dulouie/mushroom_mppt/docs/dist/pictures/beide.jpg

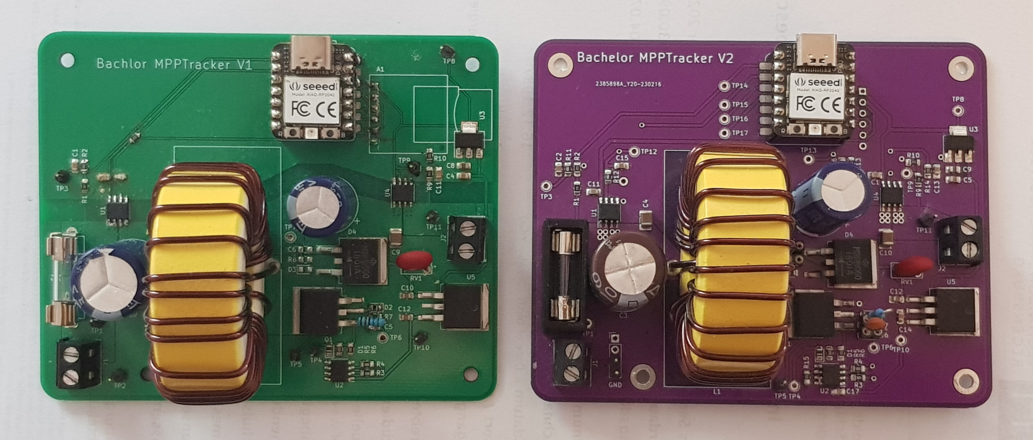
docs/dist/pictures/beide.jpg
