dulouie/mushroom_mppt/docs/dist/pictures/iu-kennlinie.png

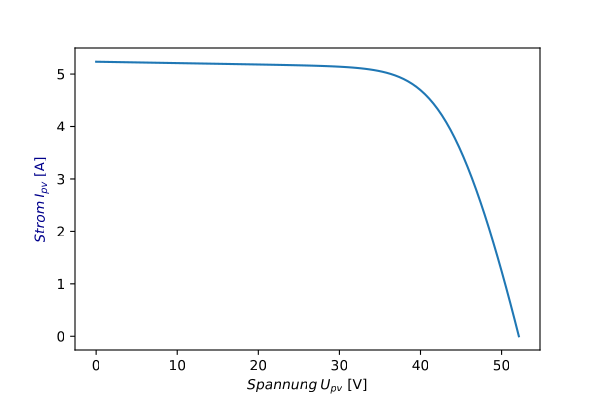
docs/dist/pictures/iu-kennlinie.png
