dulouie/mushroom_mppt/docs/dist/pictures/konzept1.png

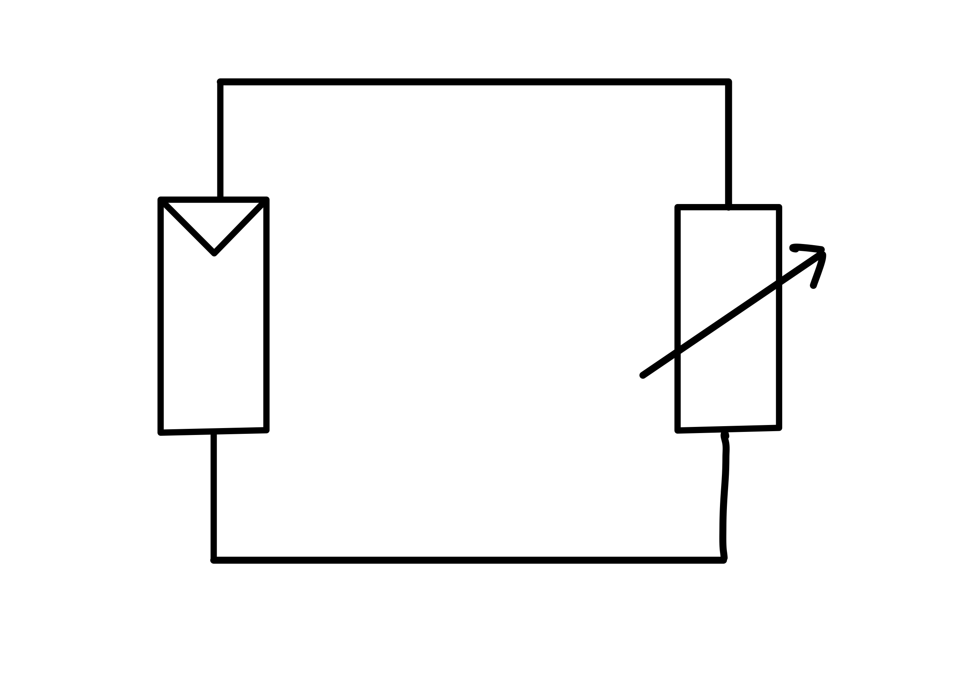
docs/dist/pictures/konzept1.png
