dulouie/mushroom_mppt/docs/dist/pictures/konzept2.png

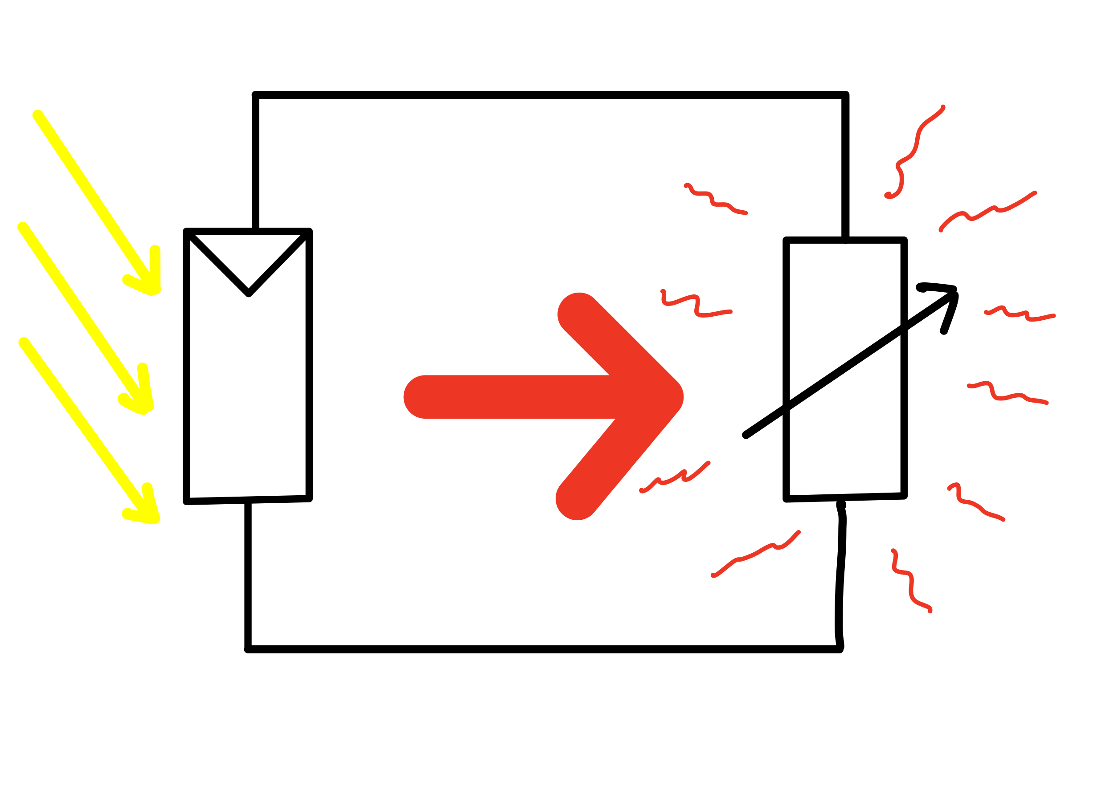
docs/dist/pictures/konzept2.png
