dulouie/mushroom_mppt/docs/dist/pictures/konzept6.png

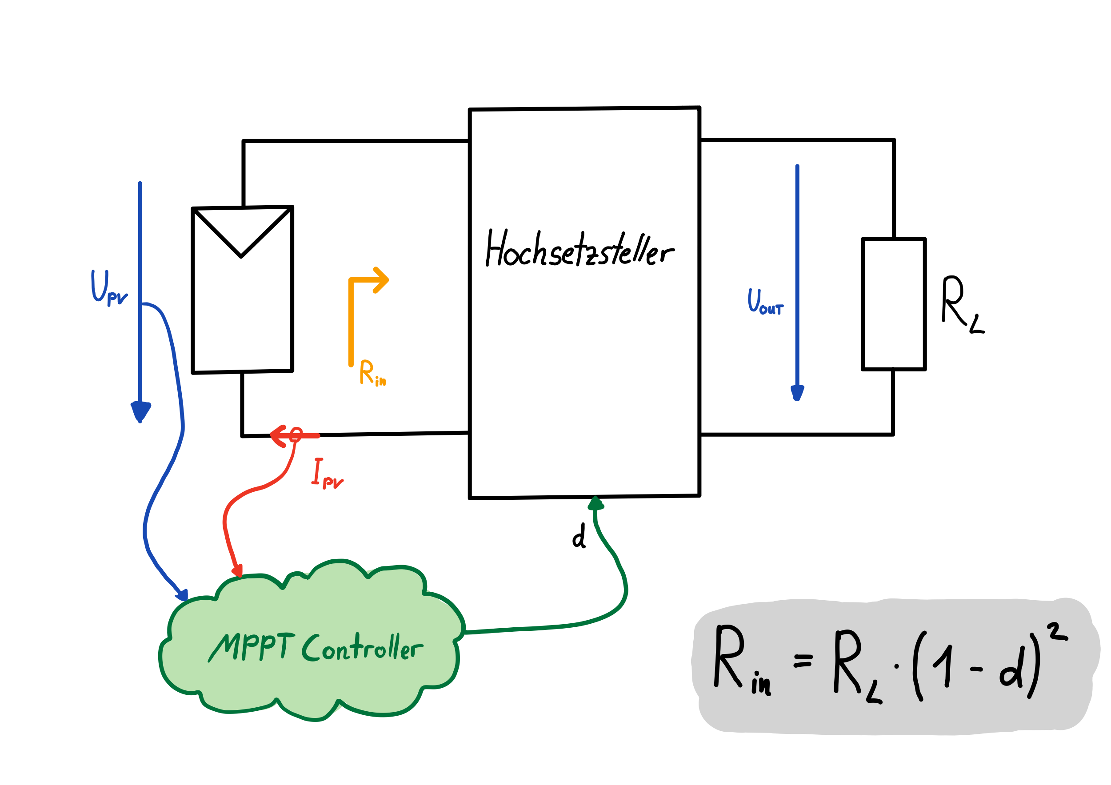
docs/dist/pictures/konzept6.png
