dulouie/mushroom_mppt/docs/dist/pictures/konzept7.png

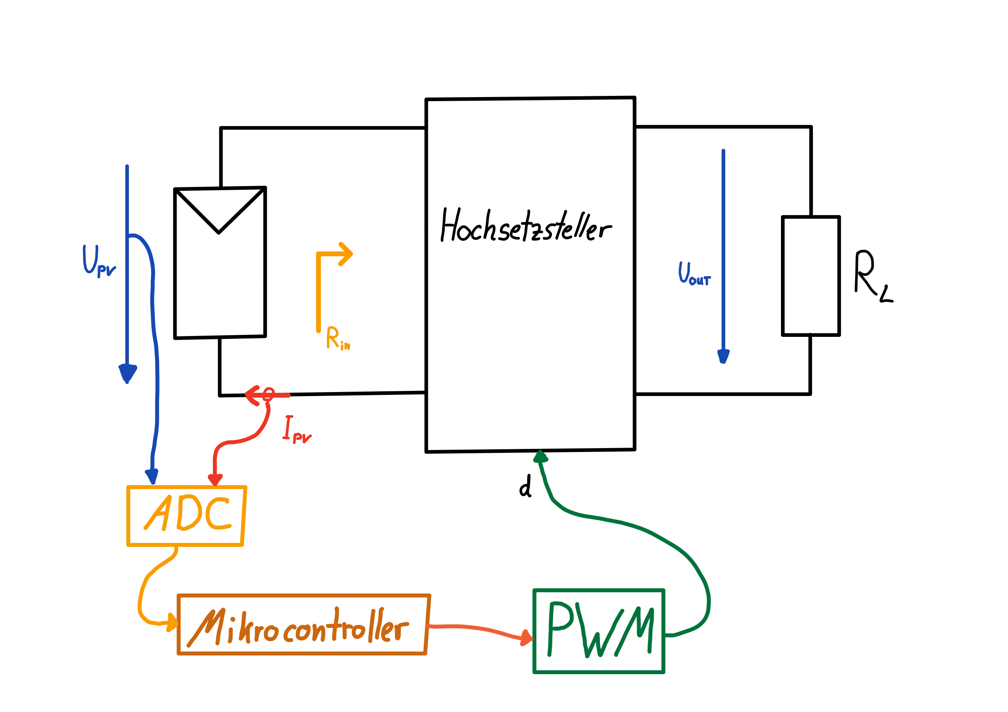
docs/dist/pictures/konzept7.png
