dulouie/mushroom_mppt/docs/dist/pictures/layout1.png

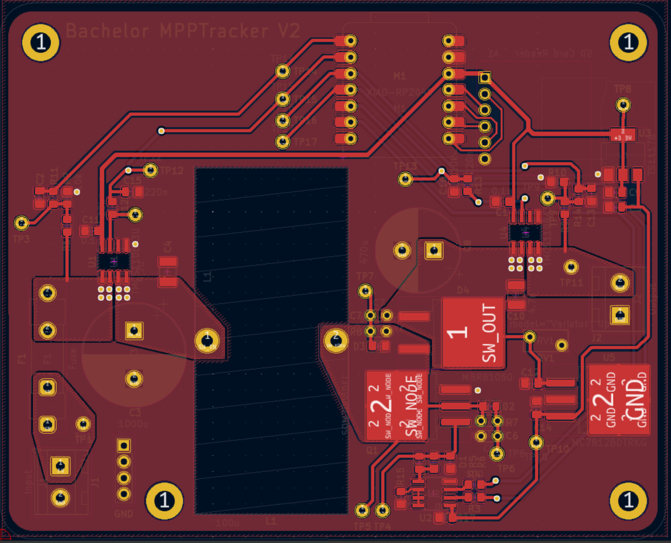
docs/dist/pictures/layout1.png
