dulouie/mushroom_mppt/docs/dist/pictures/leistungswiderstand.jpg

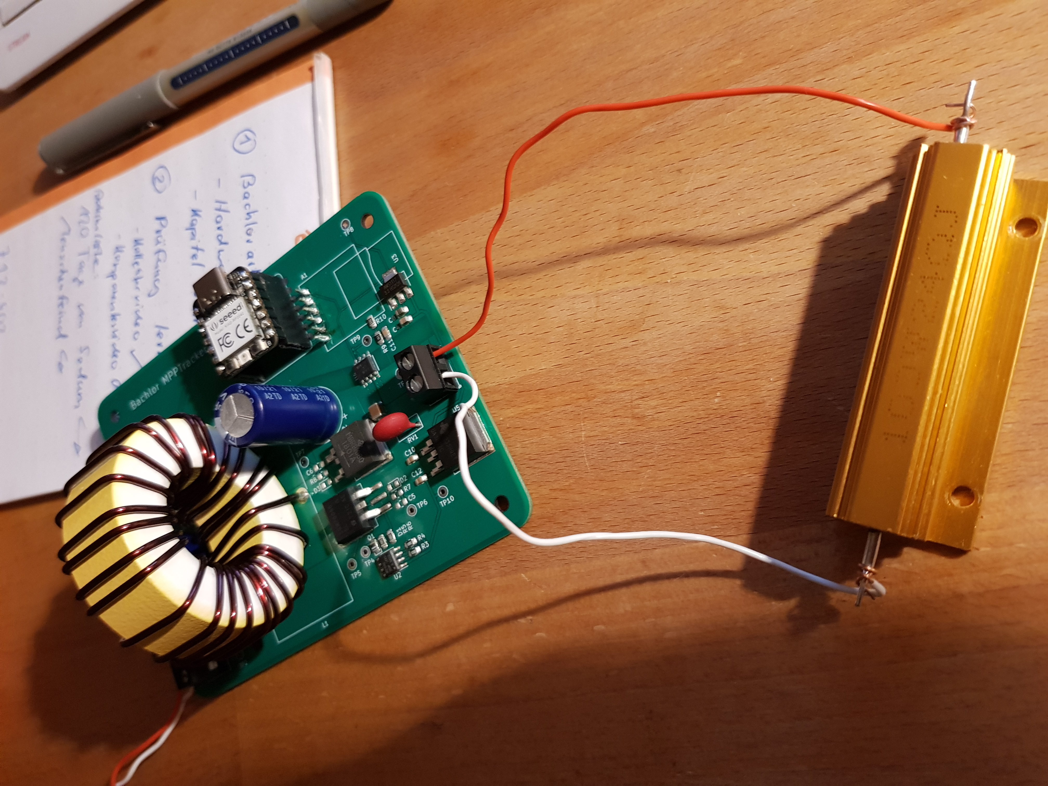
docs/dist/pictures/leistungswiderstand.jpg
