dulouie/mushroom_mppt/docs/dist/pictures/messen.jpg

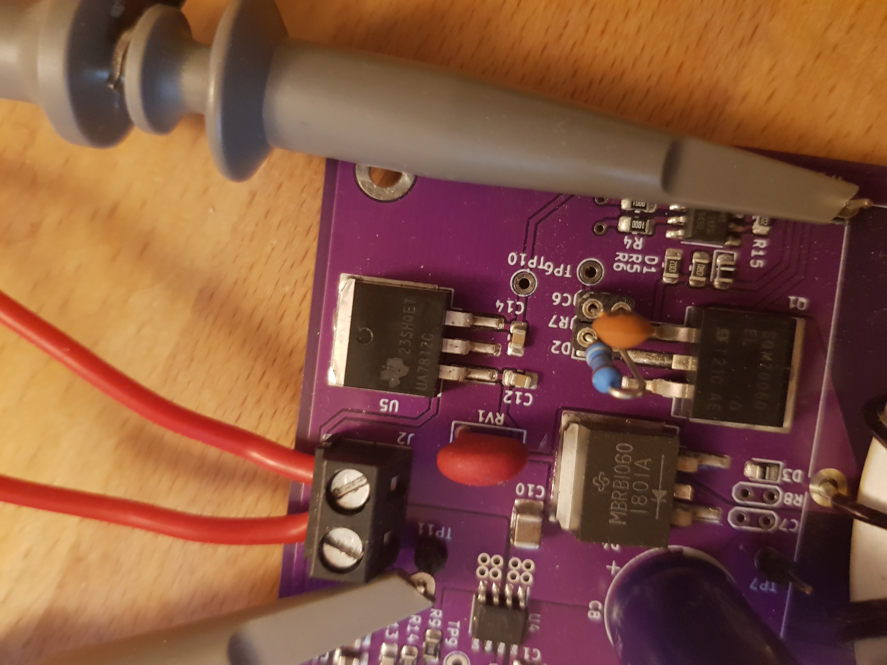
docs/dist/pictures/messen.jpg
