dulouie/mushroom_mppt/docs/dist/pictures/mosfet.jpg

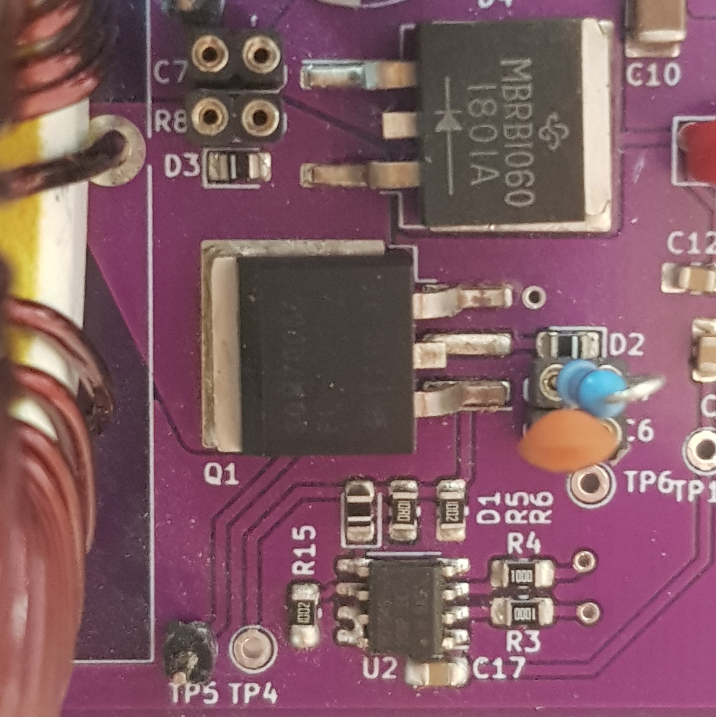
docs/dist/pictures/mosfet.jpg
