dulouie/mushroom_mppt/docs/dist/pictures/pico.jpg

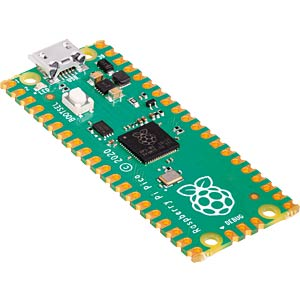
docs/dist/pictures/pico.jpg
