dulouie/mushroom_mppt/docs/dist/pictures/pvemulator.jpg

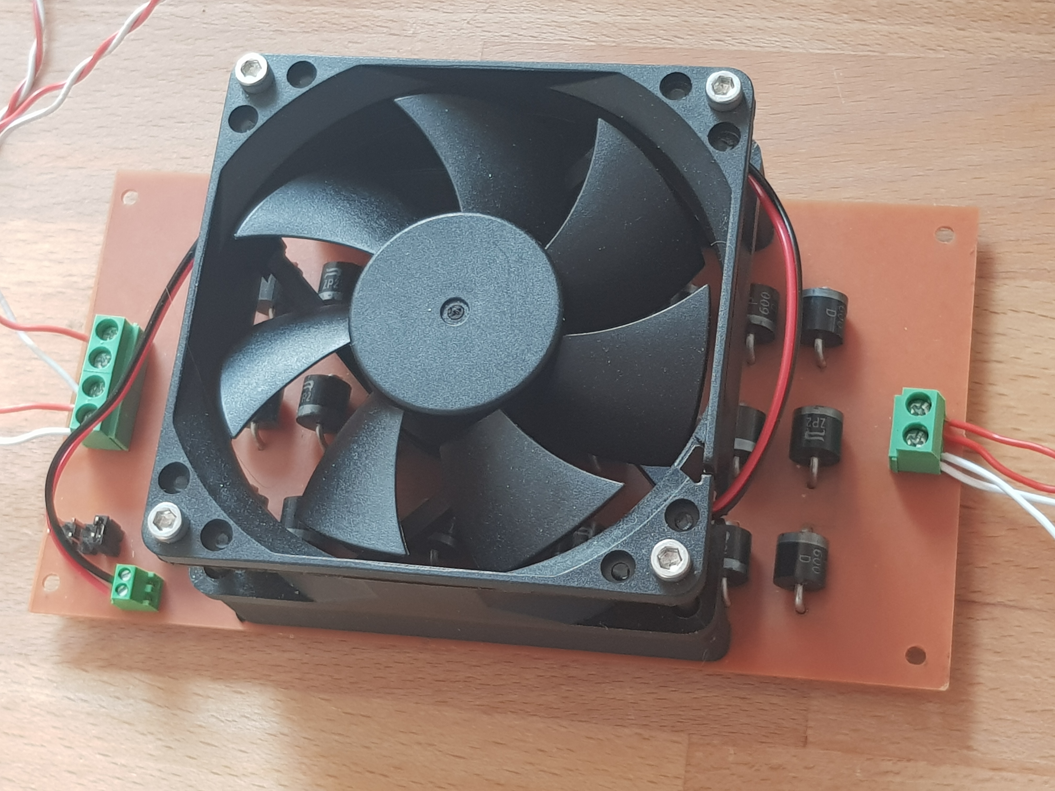
docs/dist/pictures/pvemulator.jpg
