dulouie/mushroom_mppt/docs/dist/pictures/rp2040.jpg

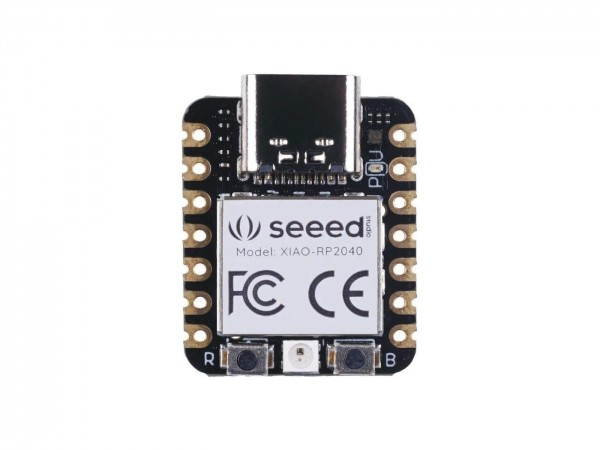
docs/dist/pictures/rp2040.jpg
