dulouie/mushroom_mppt/docs/dist/pictures/schaltplan_alt.png

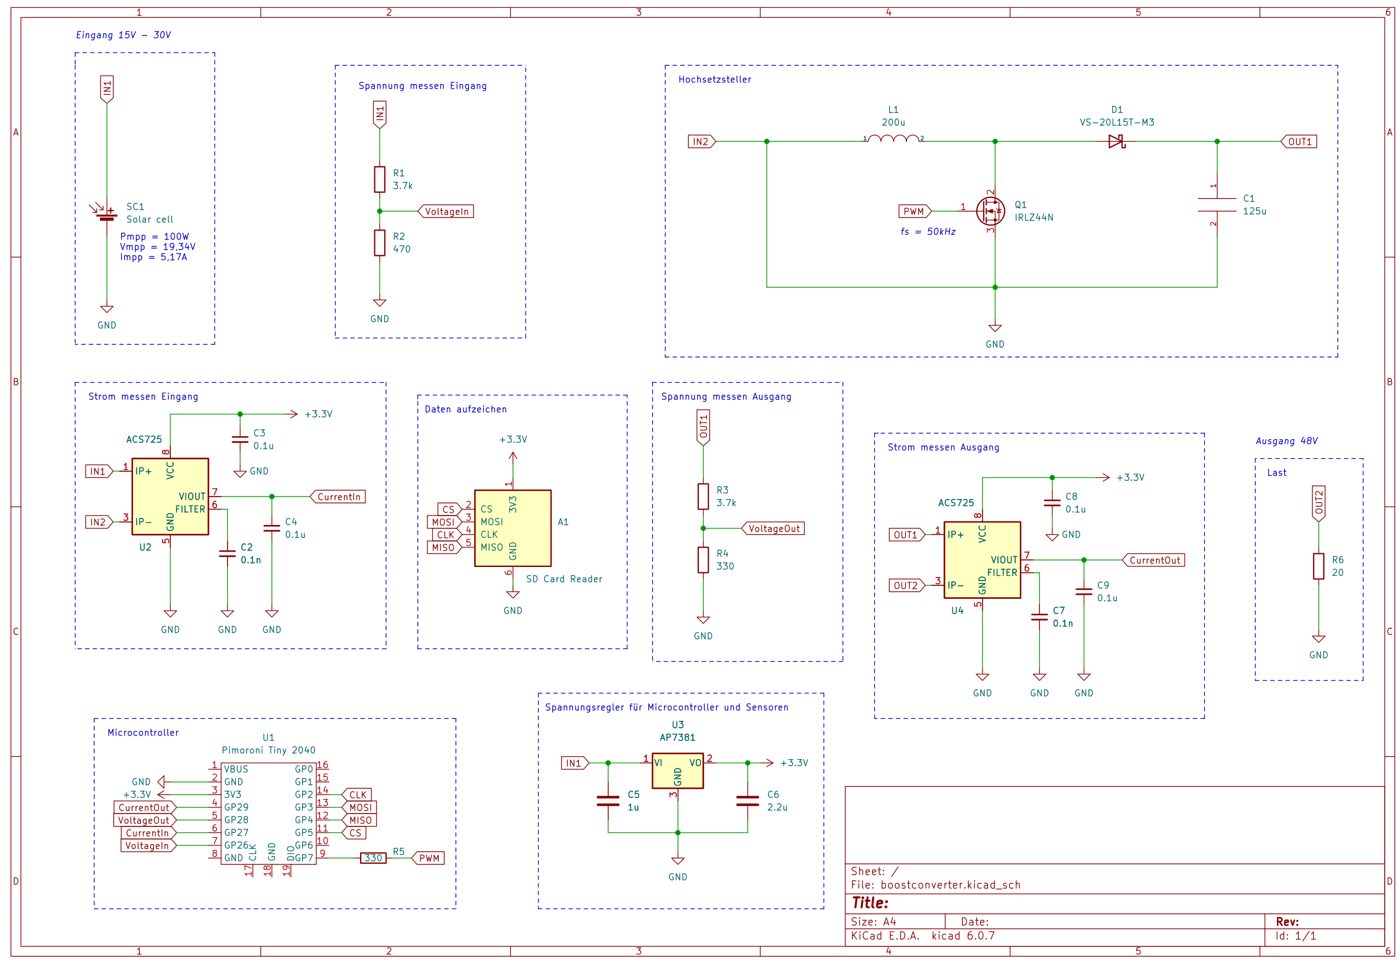
docs/dist/pictures/schaltplan_alt.png
