dulouie/mushroom_mppt/docs/dist/pictures/smd2.jpg

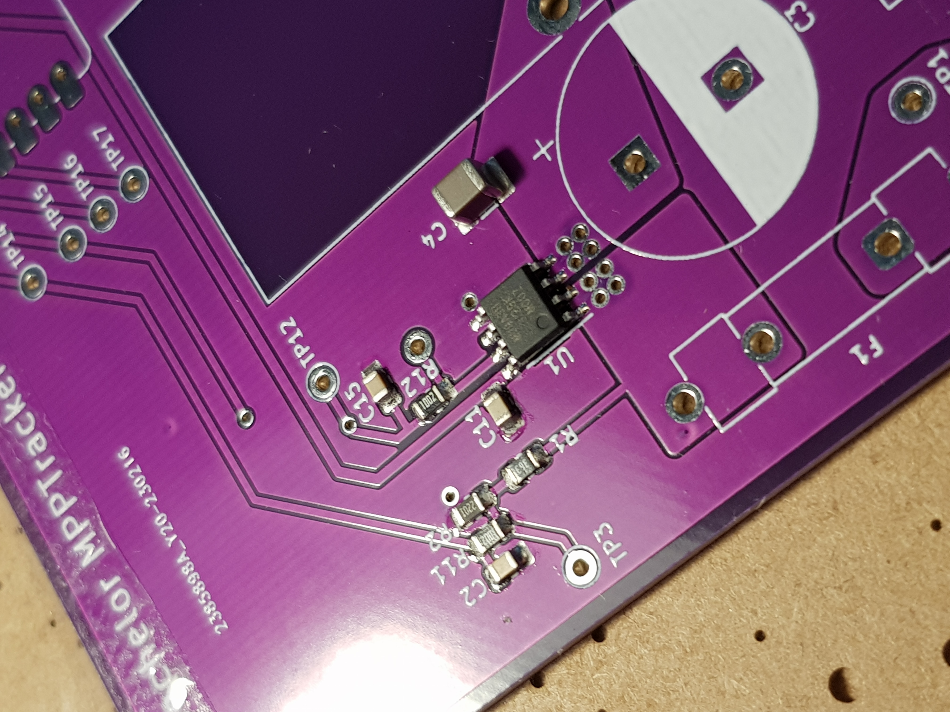
docs/dist/pictures/smd2.jpg
