dulouie/mushroom_mppt/docs/dist/pictures/smd3.jpg

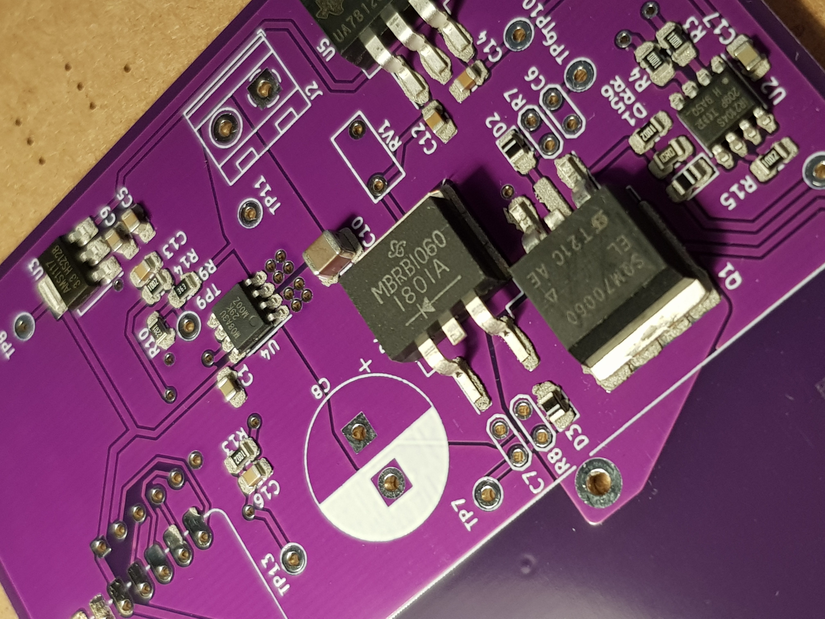
docs/dist/pictures/smd3.jpg
