dulouie/mushroom_mppt/docs/dist/pictures/smd4.jpg

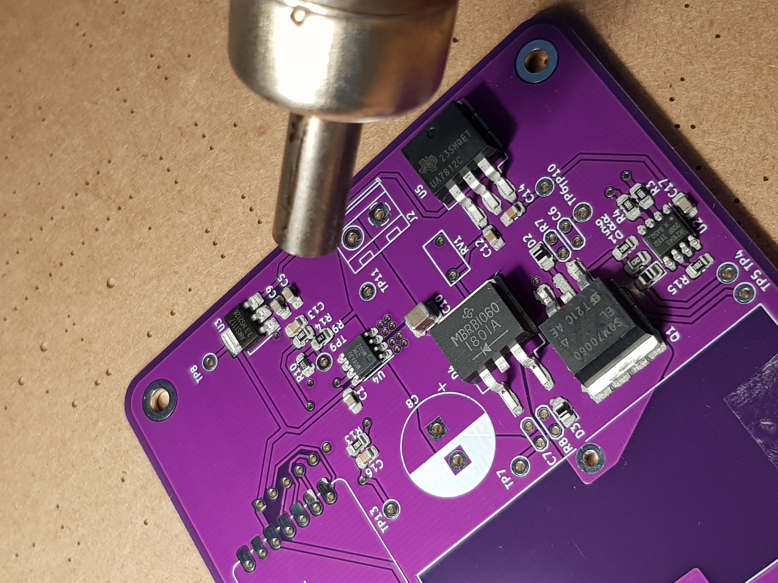
docs/dist/pictures/smd4.jpg
