dulouie/mushroom_mppt/docs/dist/pictures/snubber-ring.png

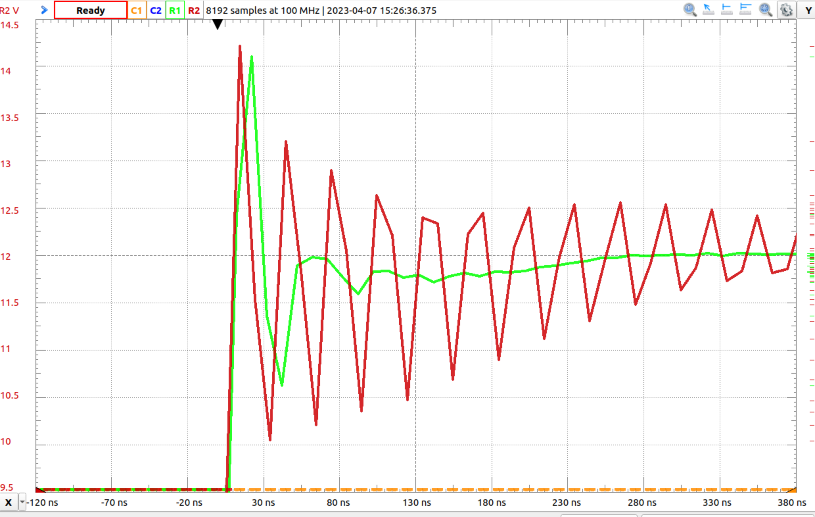
docs/dist/pictures/snubber-ring.png
