dulouie/mushroom_mppt/docs/dist/pictures/spannungsteiler.jpg

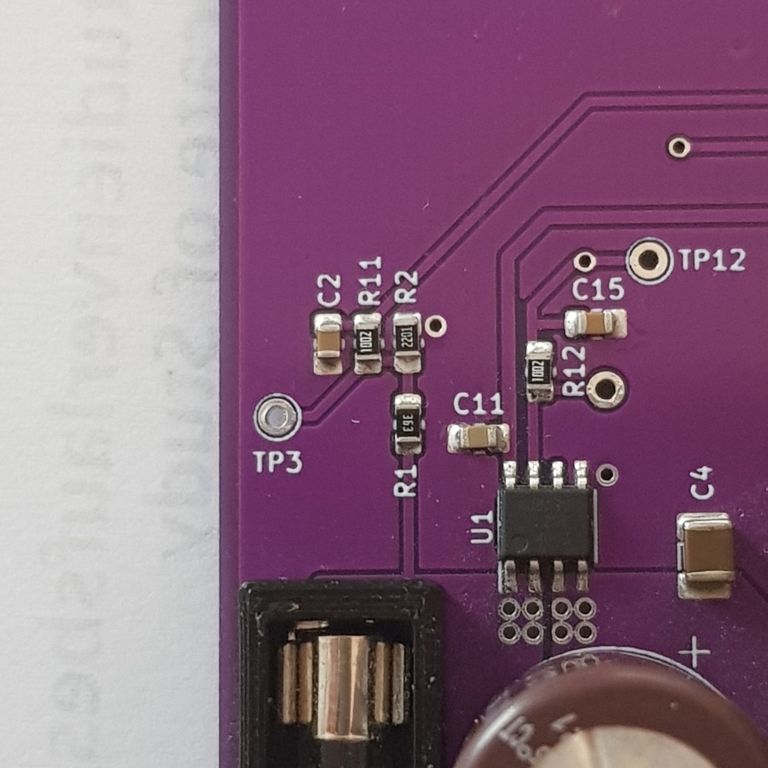
docs/dist/pictures/spannungsteiler.jpg
