dulouie/mushroom_mppt/docs/dist/pictures/tmcs1108_layout.png

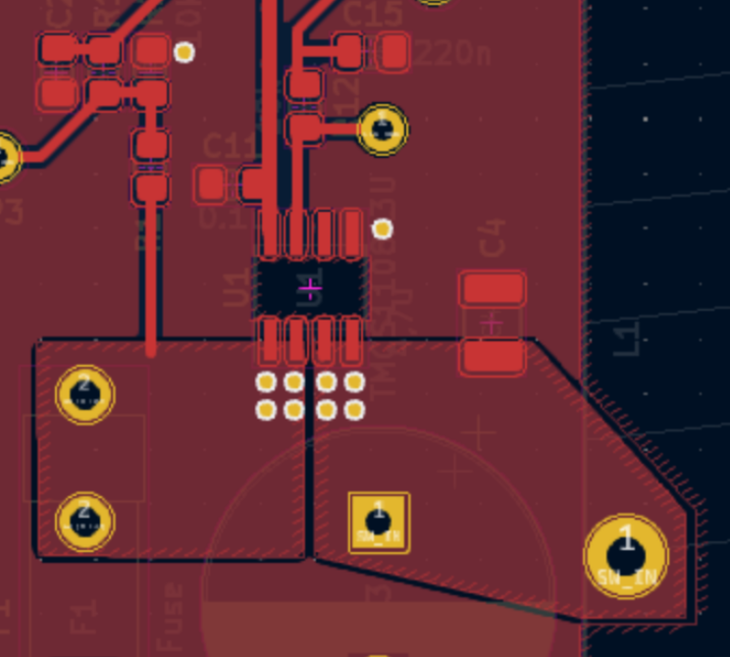
docs/dist/pictures/tmcs1108_layout.png
