dulouie/mushroom_mppt/docs/dist/pictures/tmcs_bild.jpg

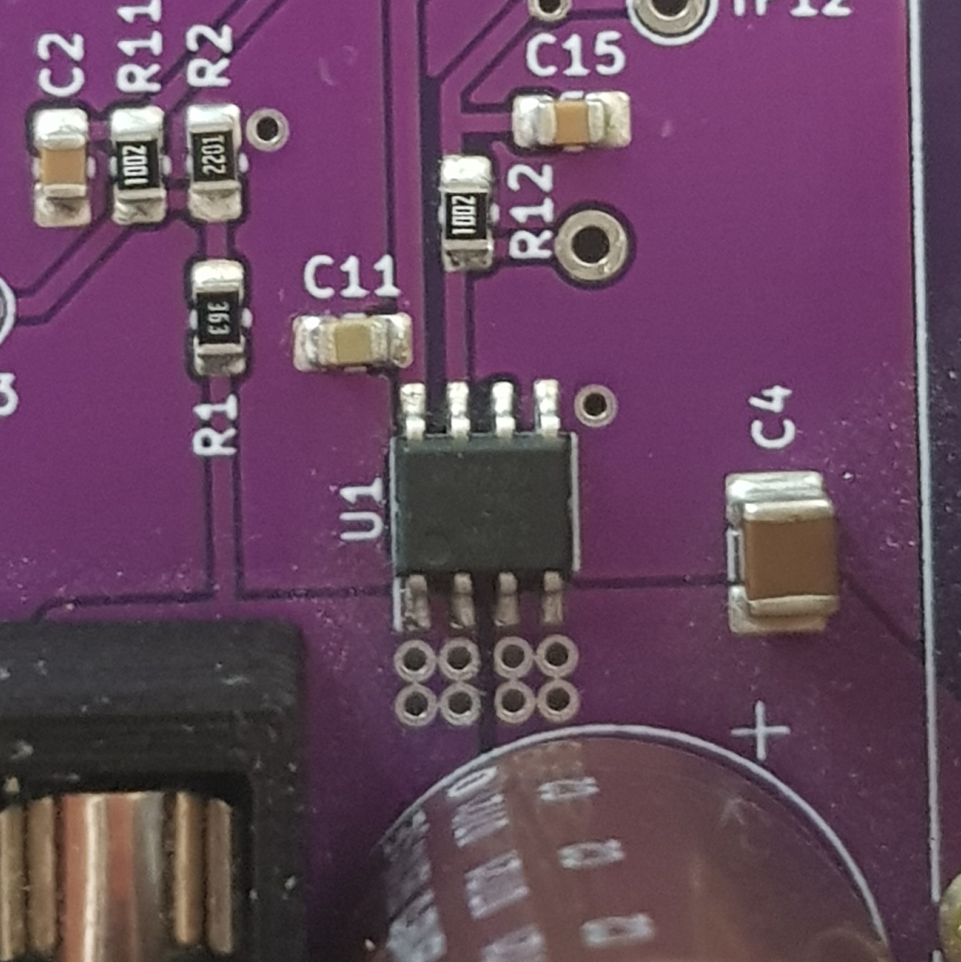
docs/dist/pictures/tmcs_bild.jpg
