dulouie/mushroom_mppt/docs/dist/pictures/treiber.jpg

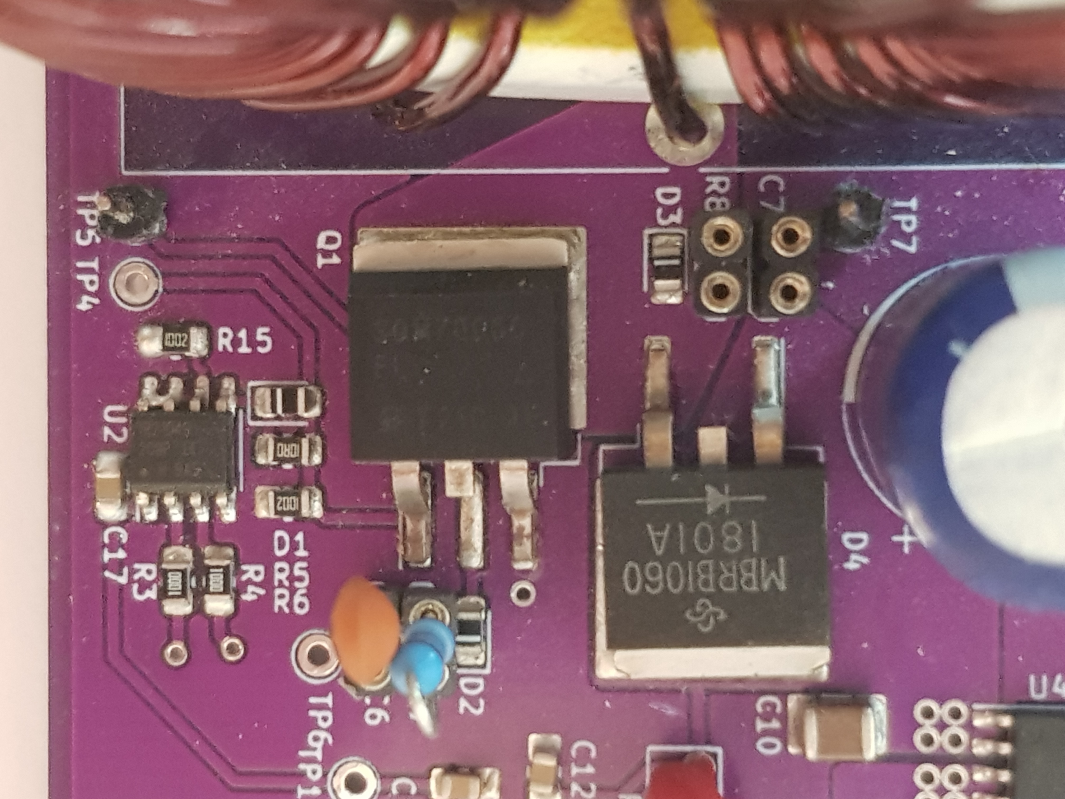
docs/dist/pictures/treiber.jpg
