dulouie/mushroom_mppt/docs/dist/pictures/versuchsaufbau.jpg

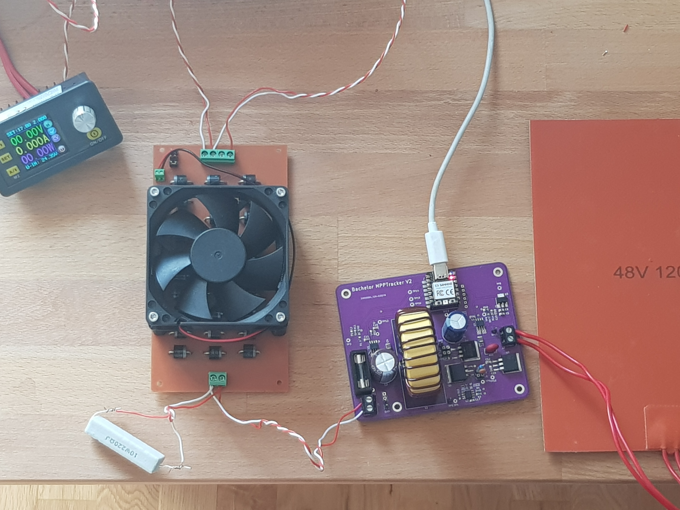
docs/dist/pictures/versuchsaufbau.jpg
