dulouie/mushroom_mppt/software/singleton.py

def singleton(cls):
    instance = None
    def getinstance(*args, **kwargs):
        nonlocal instance
        if instance is None:
            instance = cls(*args, **kwargs)
        return instance
    return getinstance
